cclrobotics/lhr-docs/Image/Design-Images-CAD/Arcturus BioCloud incub and robotic System0003.jpg

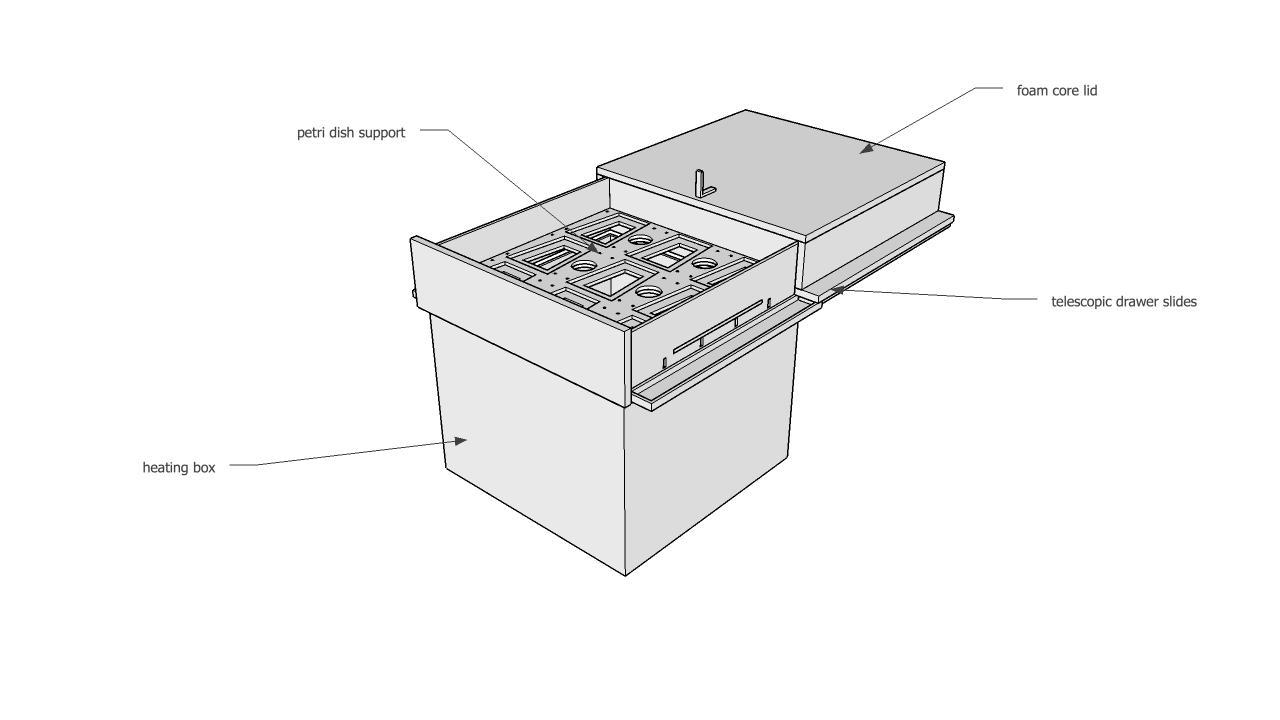
Image/Design-Images-CAD/Arcturus BioCloud incub and robotic System0003.jpg
