cclrobotics/lhr-docs/Image/Design-Images-CAD/Arcturus BioCloud incub and robotic System0007.jpg

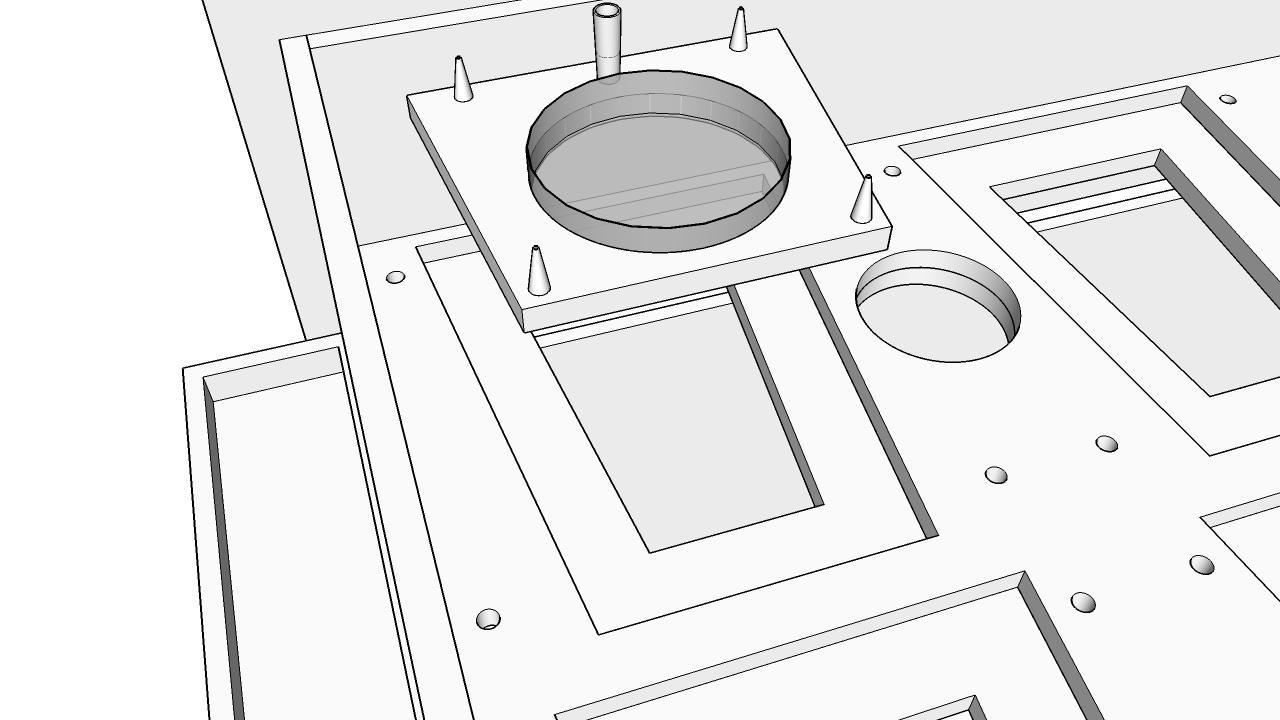
Image/Design-Images-CAD/Arcturus BioCloud incub and robotic System0007.jpg
