cclrobotics/lhr-docs/Image/Design-Images-CAD/Arcturus BioCloud incub and robotic System0010.jpg

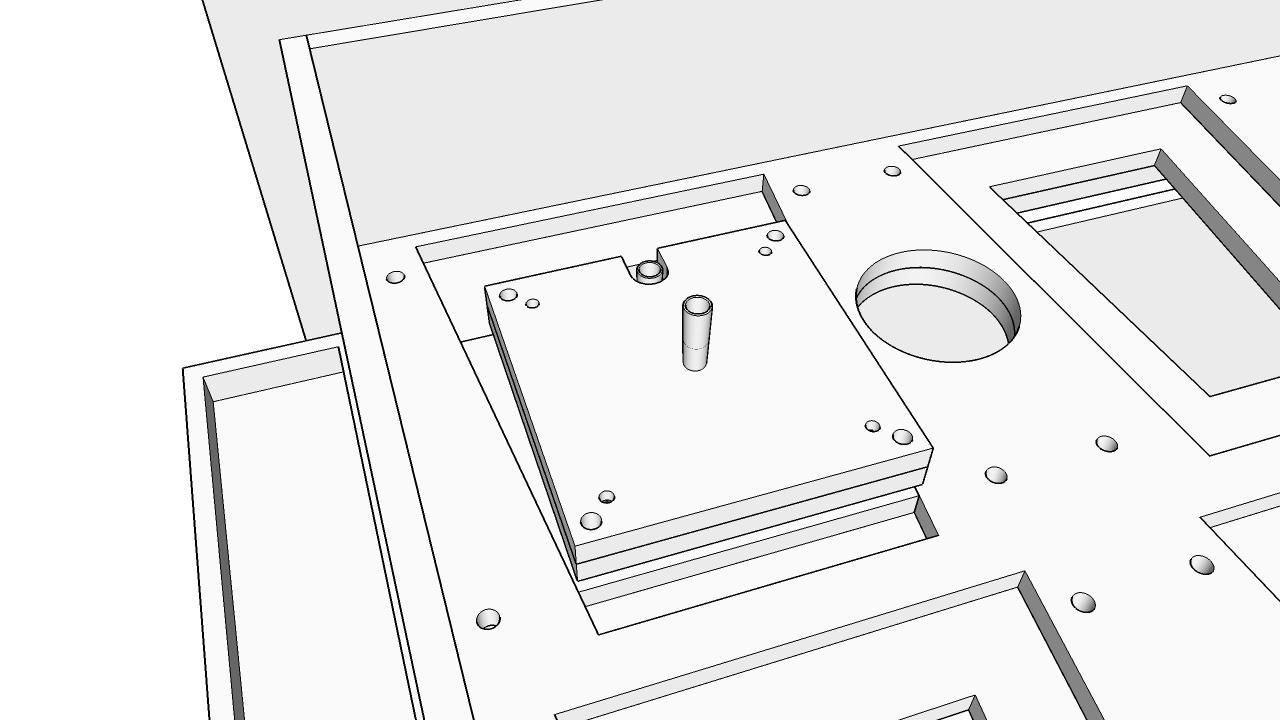
Image/Design-Images-CAD/Arcturus BioCloud incub and robotic System0010.jpg
