cclrobotics/lhr-docs/Image/Design-Images-CAD/plating tips BioServer Arcturus BioCloud0001.jpg

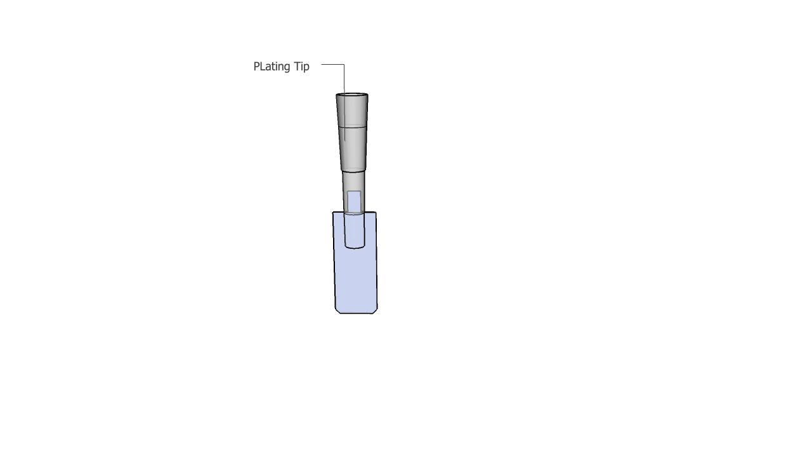
Image/Design-Images-CAD/plating tips BioServer Arcturus BioCloud0001.jpg
