cclrobotics/lhr-docs/Image/Design-Images-CAD/plating tips BioServer Arcturus BioCloud0002.jpg

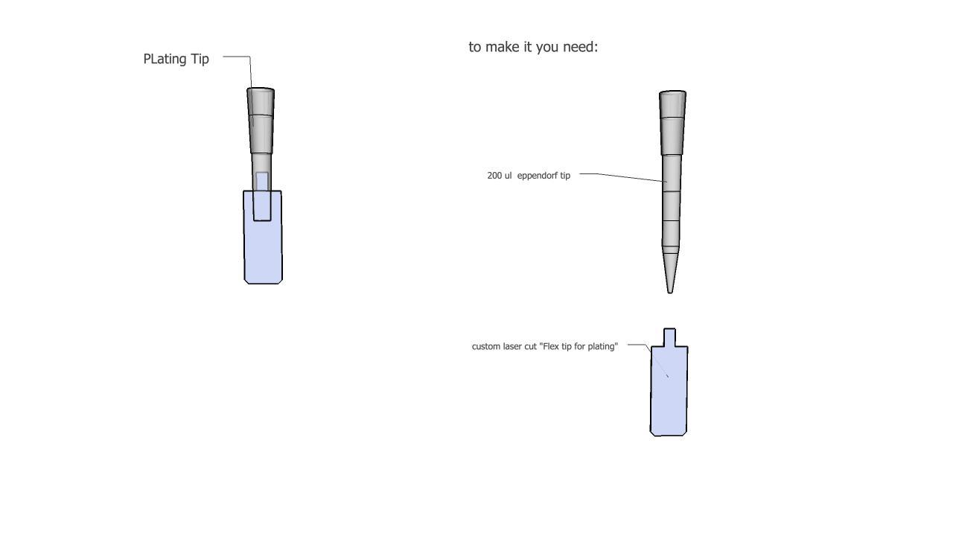
Image/Design-Images-CAD/plating tips BioServer Arcturus BioCloud0002.jpg
