cclrobotics/lhr-docs/Image/PedroSkypeImages/opentrons.png

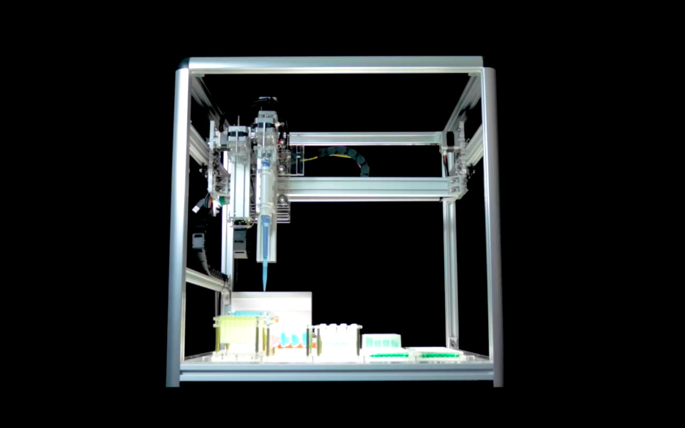
Image/PedroSkypeImages/opentrons.png
