cclrobotics/lhr-docs/Image/PedroSkypeImages/ot1.jpg

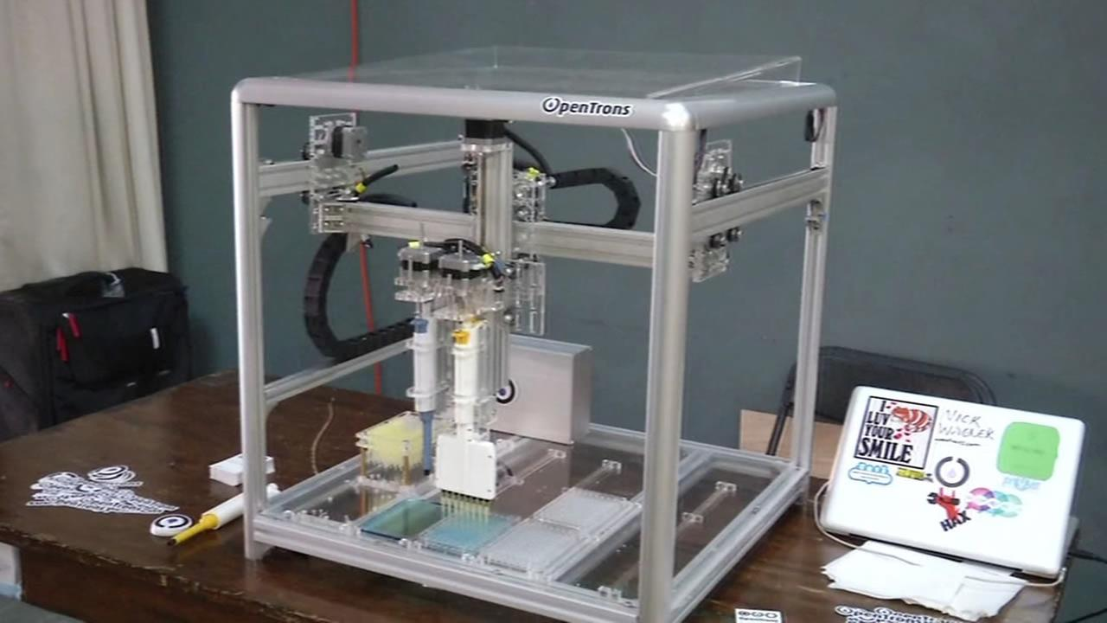
Image/PedroSkypeImages/ot1.jpg
