cclrobotics/lhr-docs/Image/PedroSkypeImages/ot2.jpeg

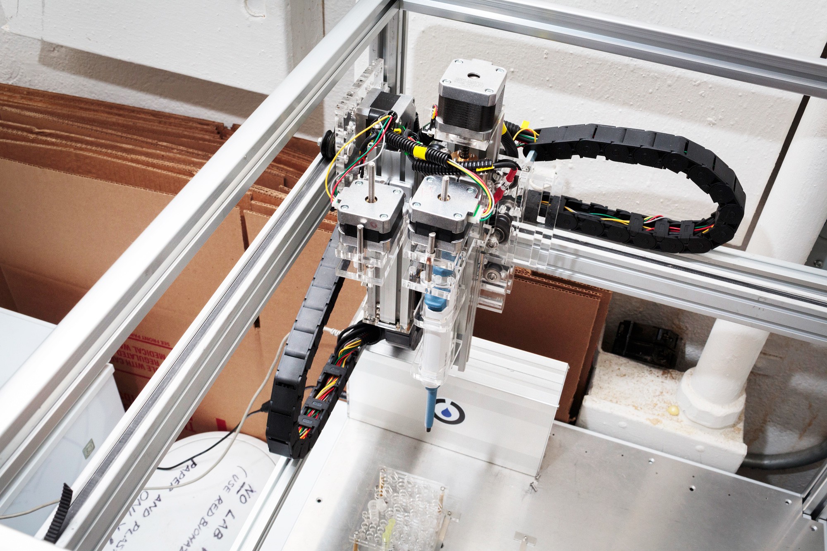
Image/PedroSkypeImages/ot2.jpeg
