cclrobotics/lhr-docs/Image/PedroSkypeImages/Pedroskype1.jpg

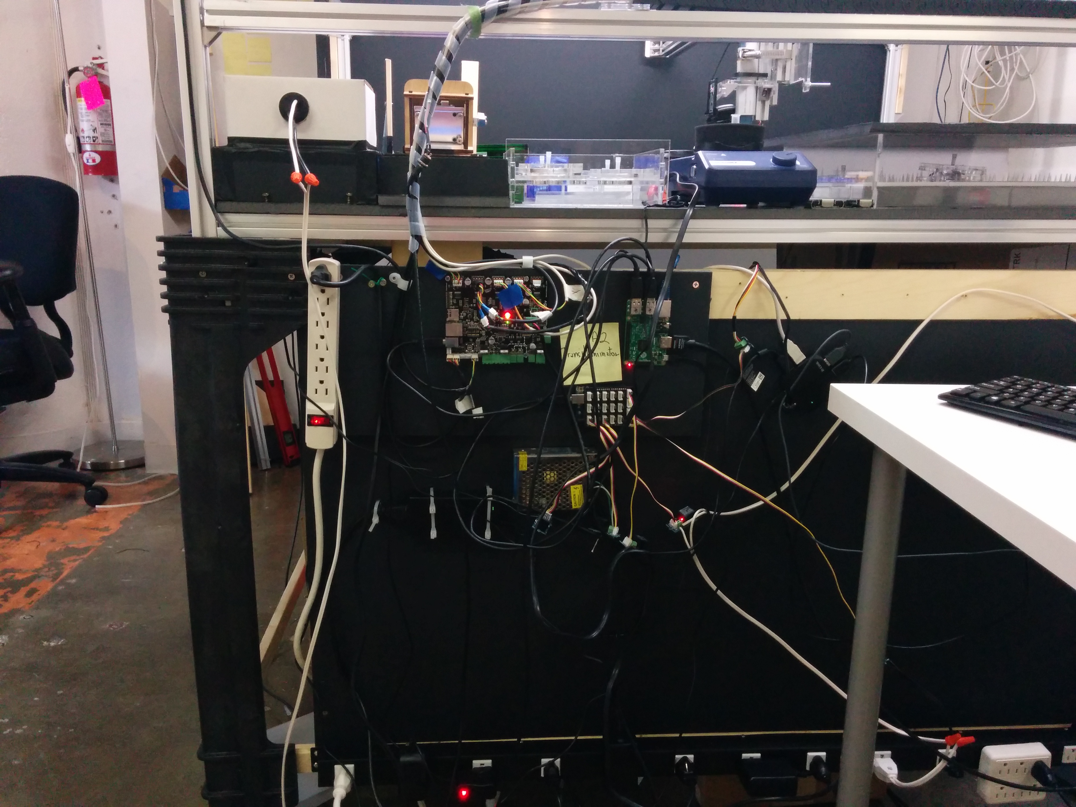
Image/PedroSkypeImages/Pedroskype1.jpg
