cclrobotics/lhr-docs/Image/PedroSkypeImages/Pedroskype2.jpg

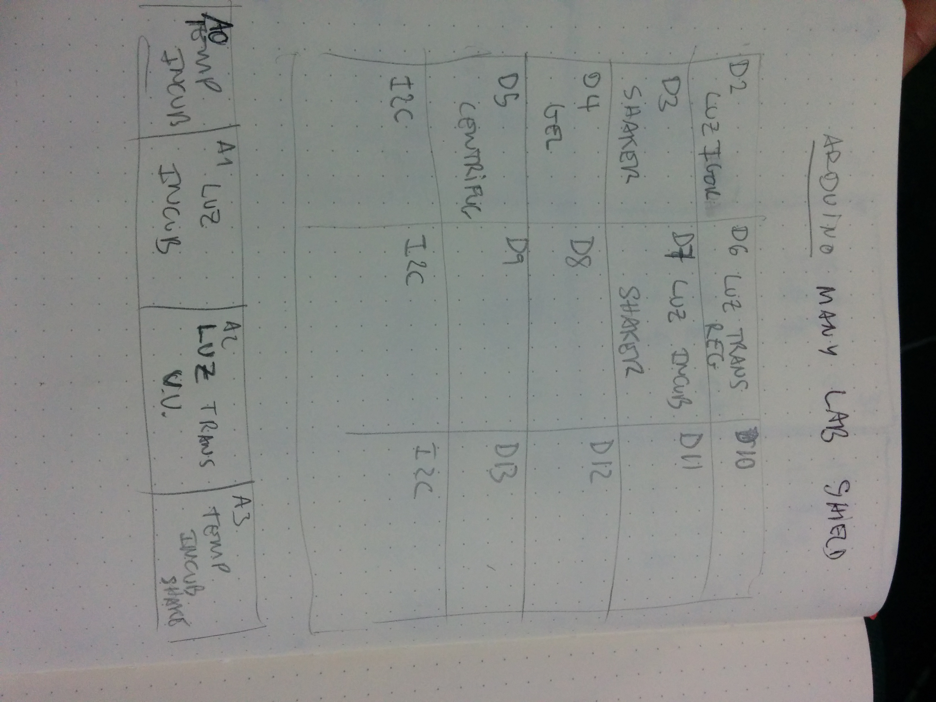
Image/PedroSkypeImages/Pedroskype2.jpg
