cclrobotics/lhr-docs/Image/PedroSkypeImages/Pedroskype4.jpg

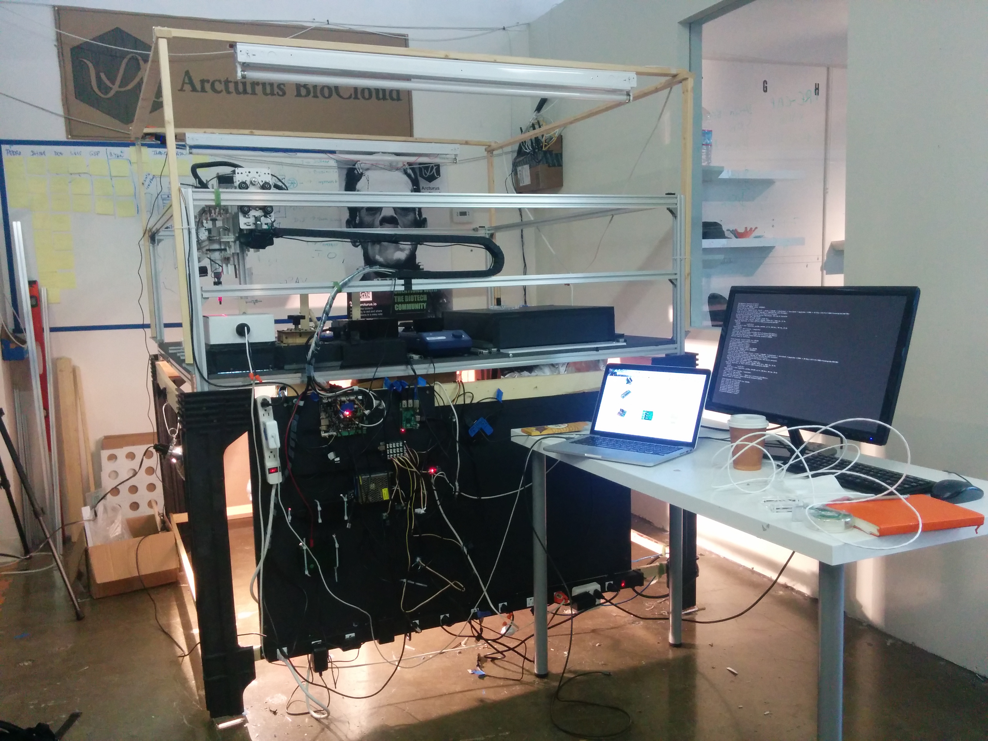
Image/PedroSkypeImages/Pedroskype4.jpg
