cclrobotics/lhr-docs/System-Diagrams/Electophoresis-System/F2IG9O8GQL8PUMA.LARGE.jpg

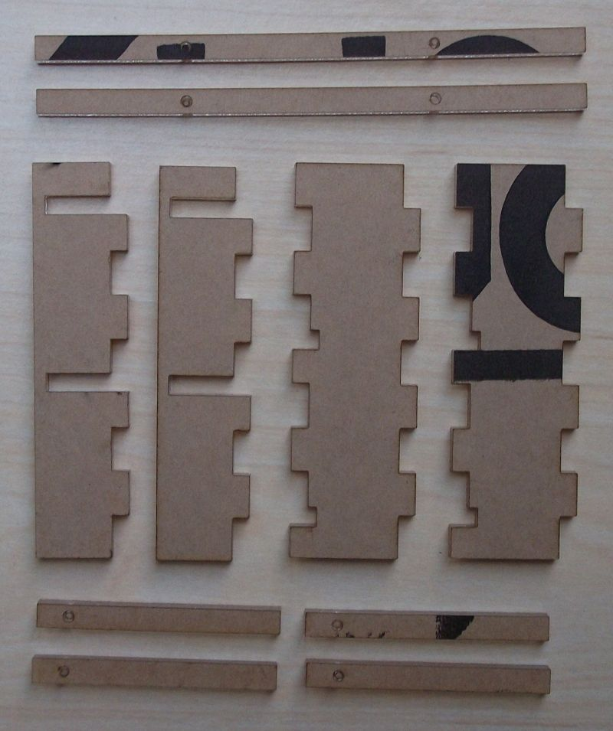
System-Diagrams/Electophoresis-System/F2IG9O8GQL8PUMA.LARGE.jpg
