cclrobotics/lhr-docs/System-Diagrams/Electophoresis-System/FIDALCZGQL8PUM4.LARGE.jpg

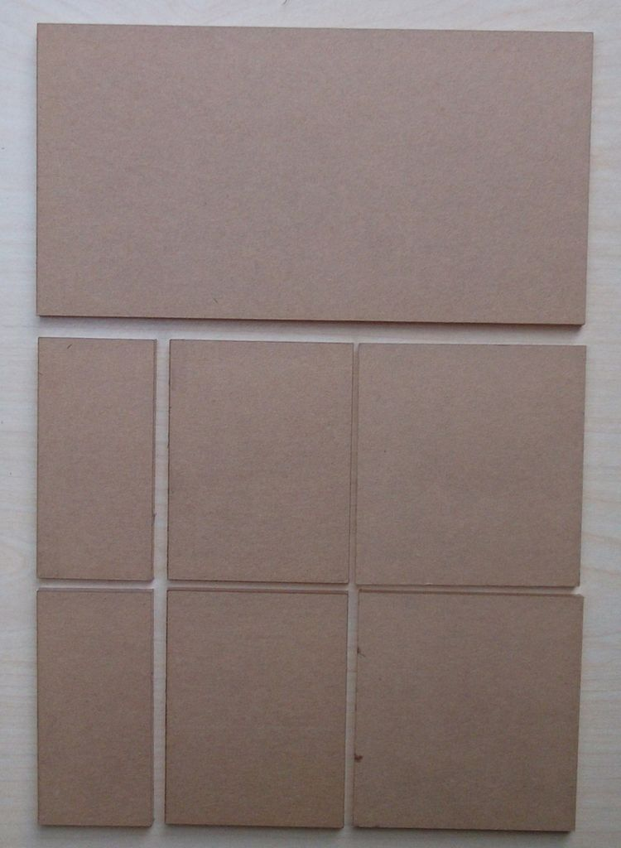
System-Diagrams/Electophoresis-System/FIDALCZGQL8PUM4.LARGE.jpg
