cclrobotics/lhr-docs/System-Diagrams/Electophoresis-System/FUEBHMSGQL8PUME.LARGE.jpg

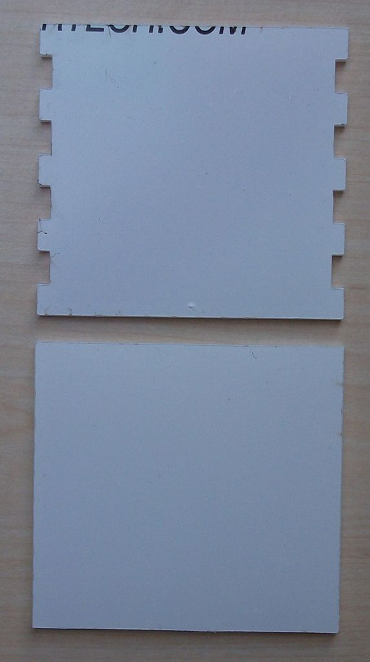
System-Diagrams/Electophoresis-System/FUEBHMSGQL8PUME.LARGE.jpg
