cclrobotics/lhr-docs/System-Diagrams/Electophoresis-System/FW3FJHMGQKLPDY4.LARGE.jpg

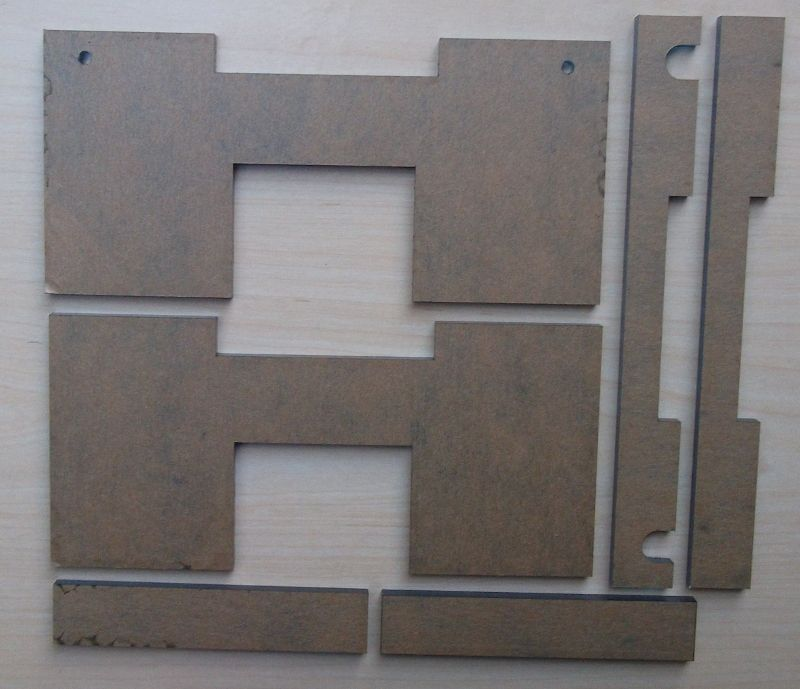
System-Diagrams/Electophoresis-System/FW3FJHMGQKLPDY4.LARGE.jpg
