cclrobotics/lhr-docs/System-Diagrams/SmoothieBoard/SmoothieBoard_diagram.png

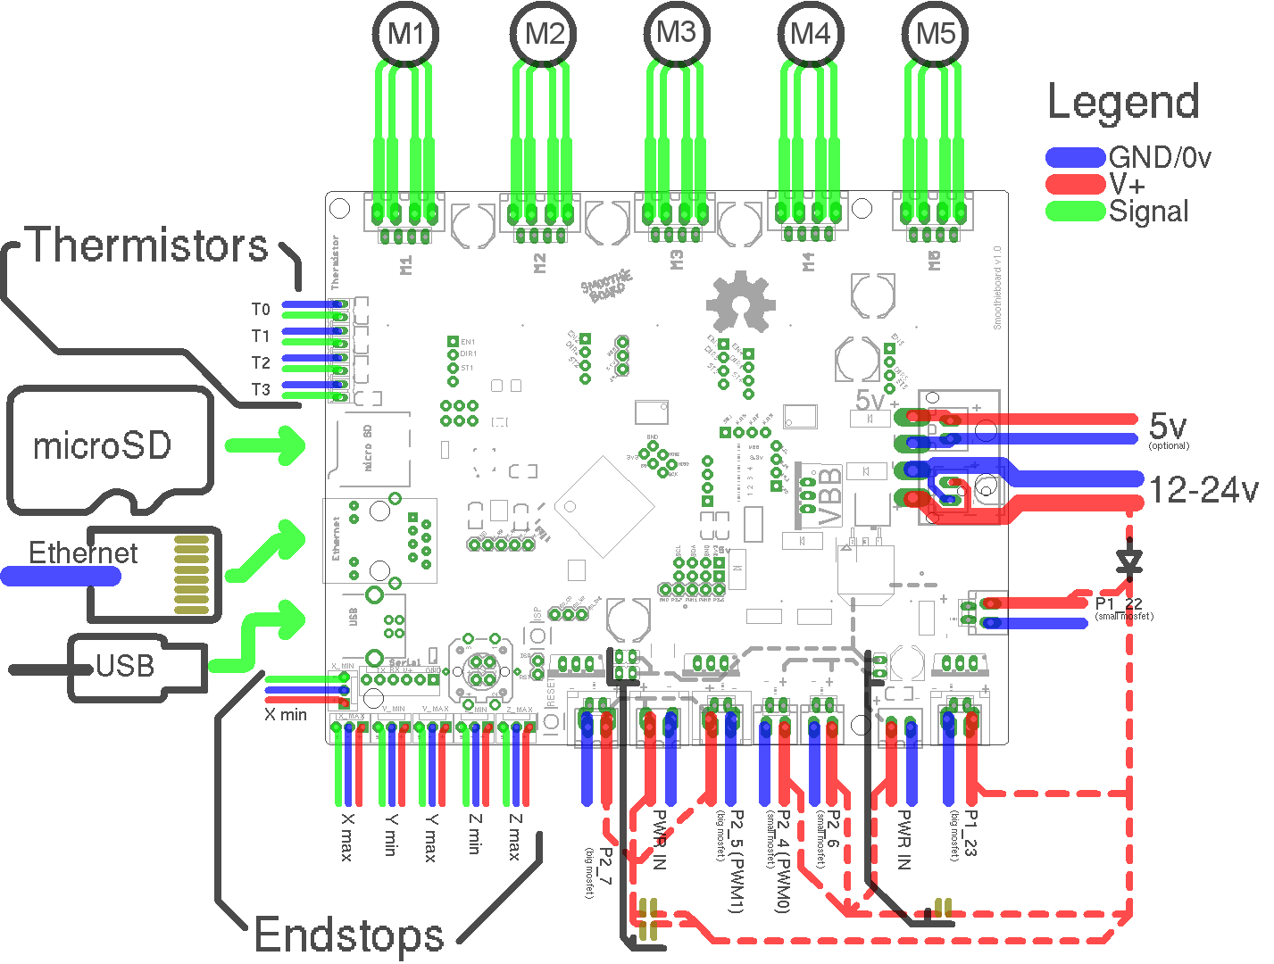
System-Diagrams/SmoothieBoard/SmoothieBoard_diagram.png
