cclrobotics/lhr-docs/Sketch-Up/bio server parts/estudo pipeta giratoria/1426054960163.jpg

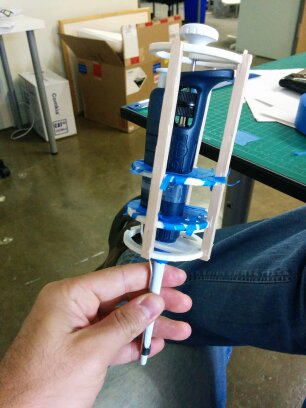
Sketch-Up/bio server parts/estudo pipeta giratoria/1426054960163.jpg
