cclrobotics/lhr-docs/Sketch-Up/bio server parts/incubadora/a/a2.dxf

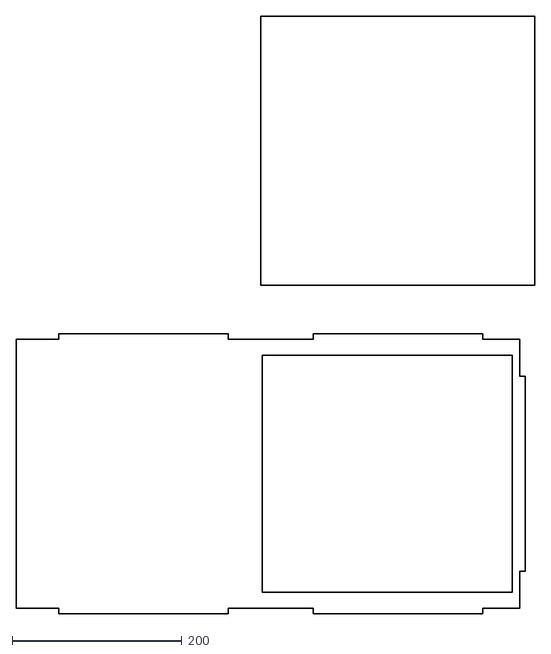
[picture p50: CAD file, 2016-08-06]
Sketch-Up/bio server parts/incubadora/a/a2.dxf
611.0 x 704.5
