cclrobotics/lhr-docs/Sketch-Up/bio server parts/incubadora/floor incubadora/pedroterra 03:11:15 - A.dxf

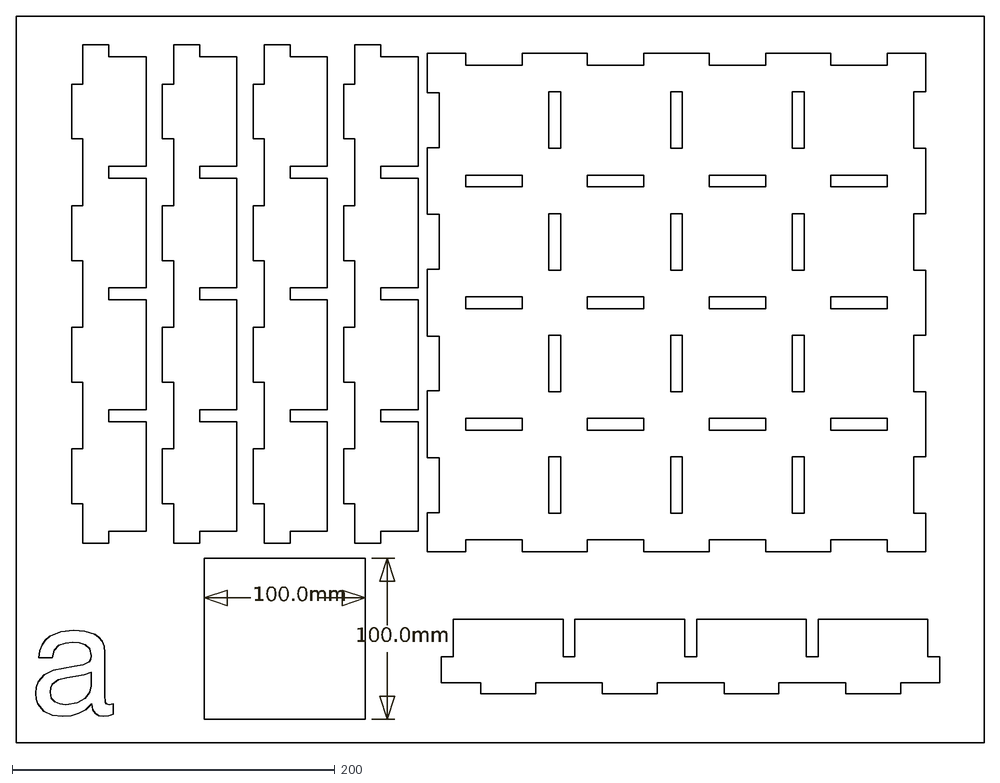
[picture p51: CAD file, 2016-08-06]
Sketch-Up/bio server parts/incubadora/floor incubadora/pedroterra 03:11:15 - A.dxf
100.0mm
