cclrobotics/lhr-docs/Sketch-Up/bio server parts/centrifuge/centrifuge container holder.obj

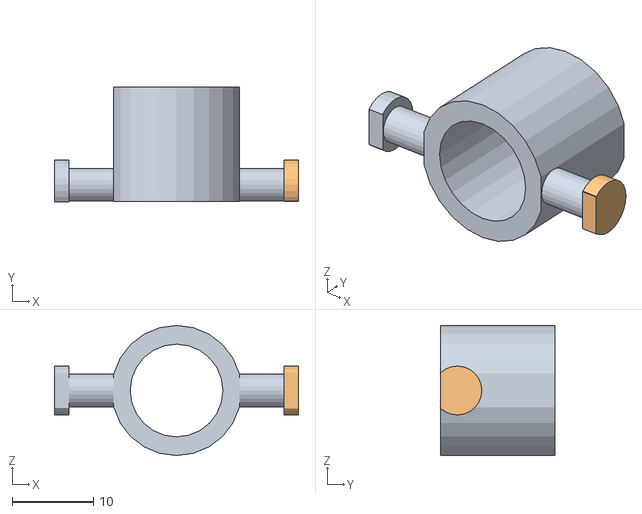
[picture p52: CAD file, 2016-08-06]
Sketch-Up/bio server parts/centrifuge/centrifuge container holder.obj
30.0 x 14.1 x 16.0
Mesh1 Component_2_1 Model
Mesh2 Component_2_1 Model
