cclrobotics/lhr-docs/Sketch-Up/bio server parts/dna holder suport/dna container lid 2.obj

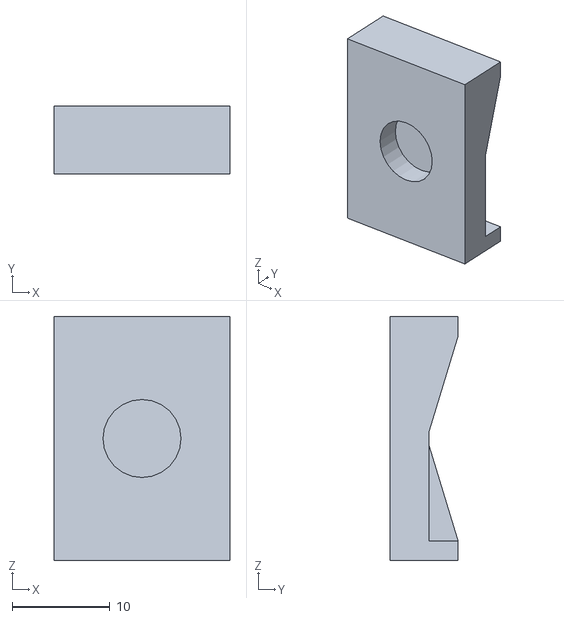
[picture p53: CAD file, 2016-08-06]
Sketch-Up/bio server parts/dna holder suport/dna container lid 2.obj
18.0 x 7.00 x 25.0
