cclrobotics/lhr-docs/Sketch-Up/bio server parts/centrifuge/centrifuge center.obj

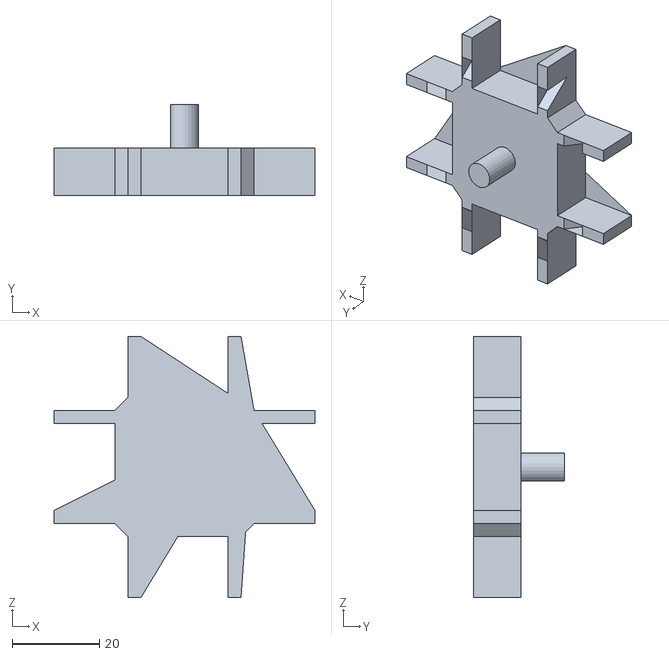
[picture p54: CAD file, 2016-08-06]
Sketch-Up/bio server parts/centrifuge/centrifuge center.obj
60.0 x 21.0 x 60.0
