cclrobotics/lhr-docs/Sketch-Up/bio server parts/dna holder suport/dna container lid.obj

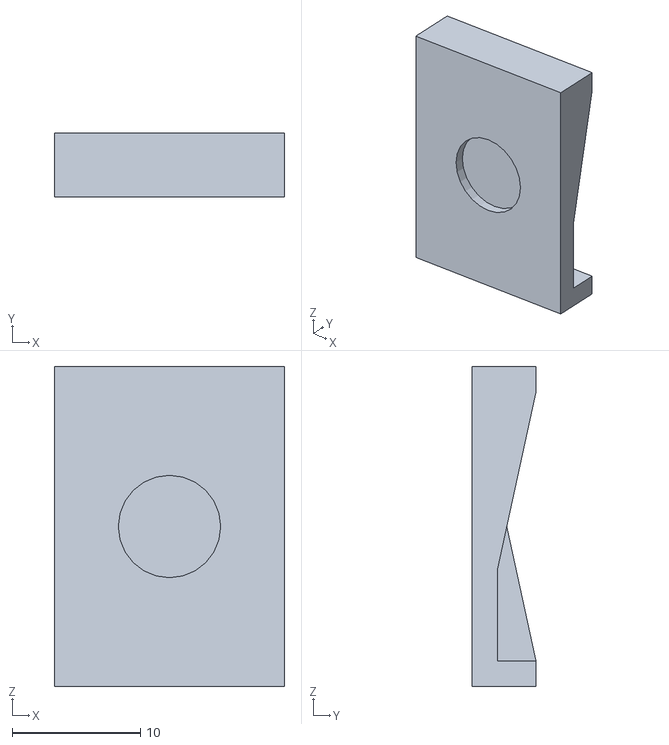
[picture p55: CAD file, 2016-08-06]
Sketch-Up/bio server parts/dna holder suport/dna container lid.obj
18.0 x 5.00 x 25.0
