cclrobotics/lhr-docs/Sketch-Up/bio server parts/centrifuge/centrifuge dna holder.obj

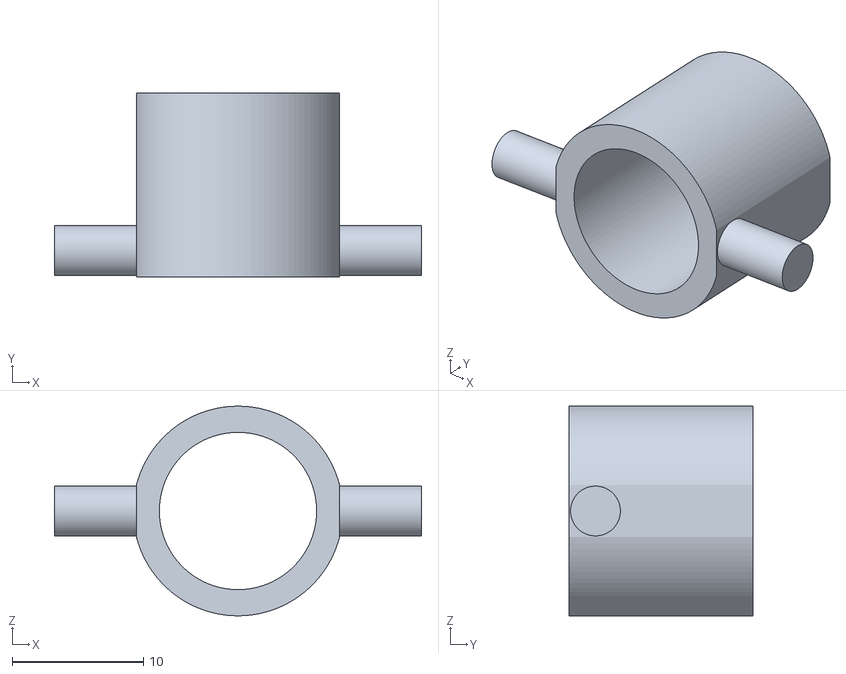
[picture p56: CAD file, 2016-08-06]
Sketch-Up/bio server parts/centrifuge/centrifuge dna holder.obj
28.0 x 14.0 x 16.0
