cclrobotics/lhr-docs/Sketch-Up/bio server parts/dna holder suport/suport container dna.obj

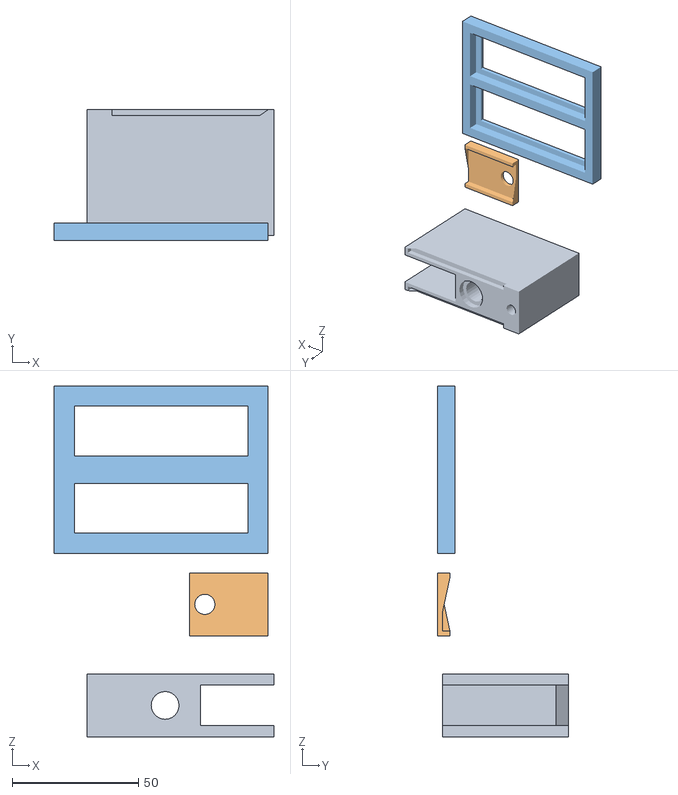
[picture p57: CAD file, 2016-08-06]
Sketch-Up/bio server parts/dna holder suport/suport container dna.obj
86.9 x 52.0 x 138.9
Mesh1 Component_2_1 Model
Mesh2 Component_3_1 Model
Mesh3 Model
