cclrobotics/lhr-docs/Sketch-Up/bio server parts/dna holder suport/dna container support.obj

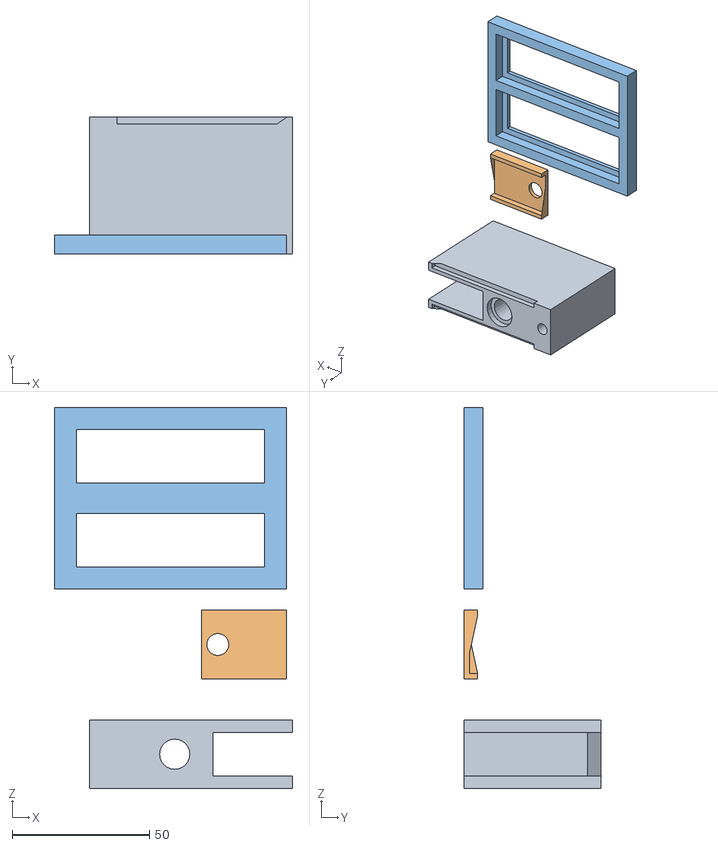
[picture p58: CAD file, 2016-08-06]
Sketch-Up/bio server parts/dna holder suport/dna container support.obj
86.9 x 50.0 x 138.9
Mesh1 Component_2_1 Model
Mesh2 Component_3_1 Model
Mesh3 Model
